tjhowse/blinker/datasheets/Supercapacitor Degradation and Life-time_files/supercapacitor-degradation-and-life-time-1140x641.jpg

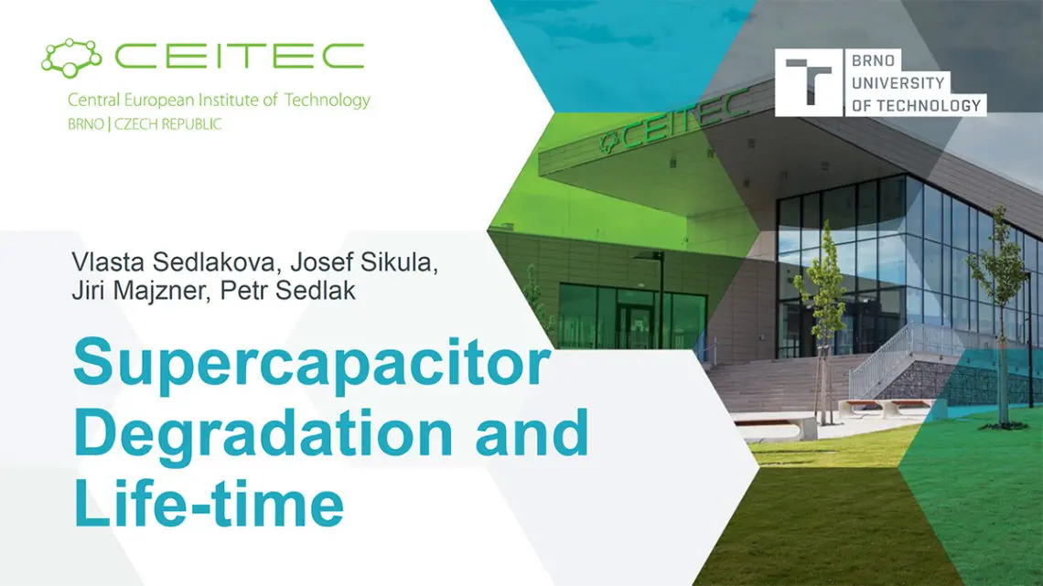
datasheets/Supercapacitor Degradation and Life-time_files/supercapacitor-degradation-and-life-time-1140x641.jpg
