tjhowse/blinker/datasheets/Supercapacitor Degradation and Life-time_files/2nd-PCNS-e-proceedings-750x595.jpg

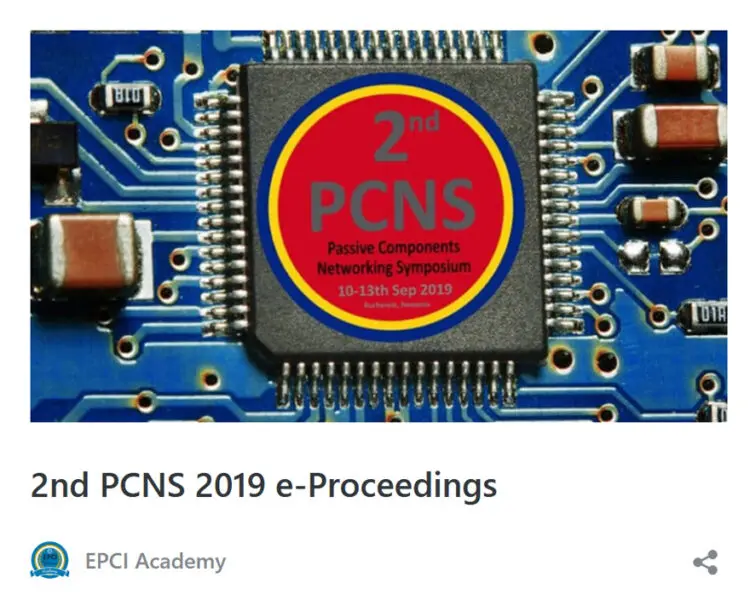
datasheets/Supercapacitor Degradation and Life-time_files/2nd-PCNS-e-proceedings-750x595.jpg
