tjhowse/blinker/datasheets/Supercapacitor Degradation and Life-time_files/CNF-MIM-world-thinnest-capacitors-350x250.jpg

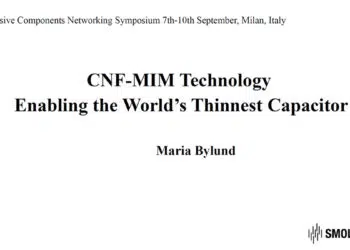
datasheets/Supercapacitor Degradation and Life-time_files/CNF-MIM-world-thinnest-capacitors-350x250.jpg
