tjhowse/blinker/datasheets/Supercapacitor Degradation and Life-time_files/development-of-3D-on-chip-capacitor-350x250.jpg

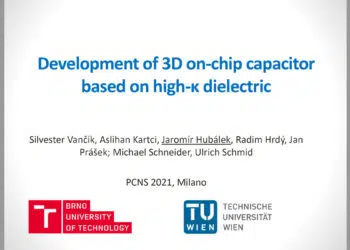
datasheets/Supercapacitor Degradation and Life-time_files/development-of-3D-on-chip-capacitor-350x250.jpg
