tjhowse/blinker/datasheets/Supercapacitor Degradation and Life-time_files/Fig1-supercapacitor-equivalent-circuit-model-300x136.png

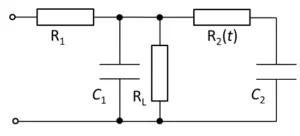
datasheets/Supercapacitor Degradation and Life-time_files/Fig1-supercapacitor-equivalent-circuit-model-300x136.png
