tjhowse/blinker/datasheets/Supercapacitor Degradation and Life-time_files/Fig-2a-supercapacitor-Helmholtz-capacitance-vs-time-of-a_002.png

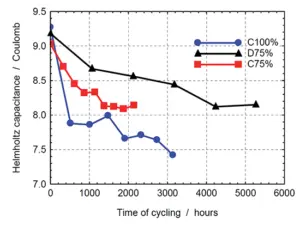
datasheets/Supercapacitor Degradation and Life-time_files/Fig-2a-supercapacitor-Helmholtz-capacitance-vs-time-of-a_002.png
