tjhowse/blinker/datasheets/Supercapacitor Degradation and Life-time_files/Fig-2b-supercapacitor-diffuse-capacitance-vs-time-of-age_002.png

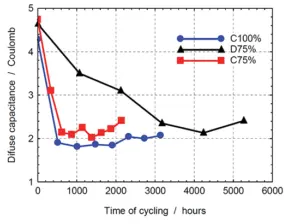
datasheets/Supercapacitor Degradation and Life-time_files/Fig-2b-supercapacitor-diffuse-capacitance-vs-time-of-age_002.png
