tjhowse/blinker/datasheets/Supercapacitor Degradation and Life-time_files/Fig-2b-supercapacitor-diffuse-capacitance-vs-time-of-ageing-.png

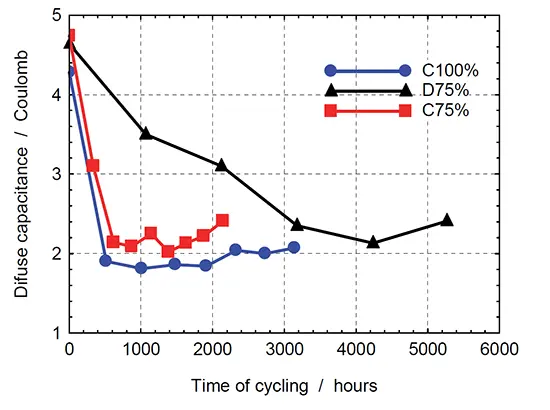
datasheets/Supercapacitor Degradation and Life-time_files/Fig-2b-supercapacitor-diffuse-capacitance-vs-time-of-ageing-.png
