tjhowse/blinker/datasheets/Supercapacitor Degradation and Life-time_files/Fig-3a-supercapacitor-diffuse-resistance-parameter-vs-ti_002.png

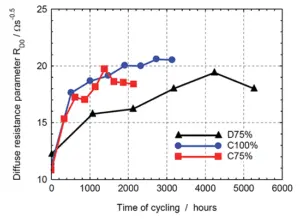
datasheets/Supercapacitor Degradation and Life-time_files/Fig-3a-supercapacitor-diffuse-resistance-parameter-vs-ti_002.png
