tjhowse/blinker/datasheets/Supercapacitor Degradation and Life-time_files/Fig-3b-supercapacitor-equivalent-series-resistance-vs-ti_002.png

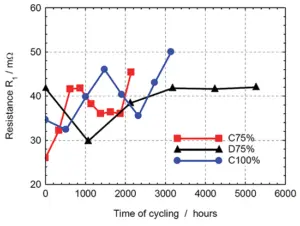
datasheets/Supercapacitor Degradation and Life-time_files/Fig-3b-supercapacitor-equivalent-series-resistance-vs-ti_002.png
