tjhowse/blinker/datasheets/Supercapacitor Degradation and Life-time_files/Fig-3b-supercapacitor-equivalent-series-resistance-vs-time-o.png

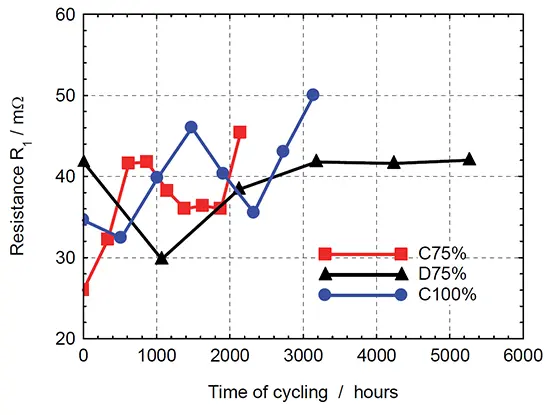
datasheets/Supercapacitor Degradation and Life-time_files/Fig-3b-supercapacitor-equivalent-series-resistance-vs-time-o.png
