tjhowse/blinker/datasheets/Supercapacitor Degradation and Life-time_files/Fig-6a-supercapacitor-DC-capacitance-vs-time-of-ageing-f_002.png

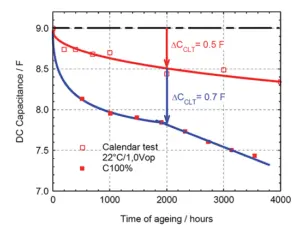
datasheets/Supercapacitor Degradation and Life-time_files/Fig-6a-supercapacitor-DC-capacitance-vs-time-of-ageing-f_002.png
