tjhowse/blinker/datasheets/Supercapacitor Degradation and Life-time_files/Fig-8-supercapacitor-DC-capacitance-relative-value-vs-ti_002.png

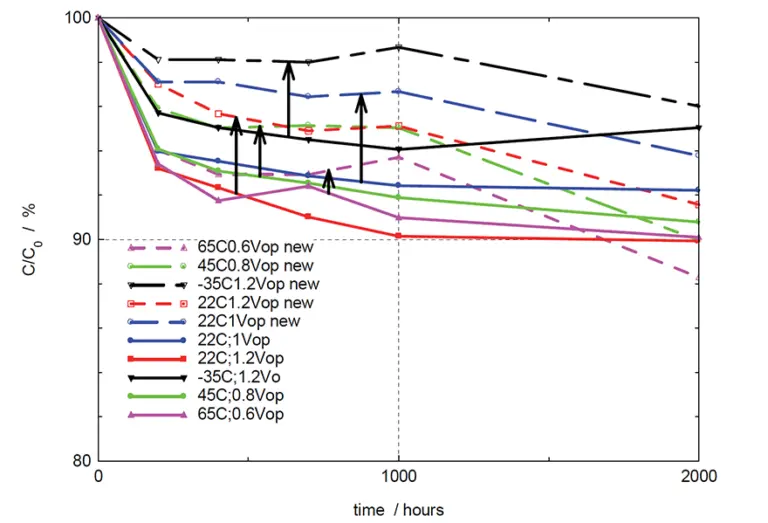
datasheets/Supercapacitor Degradation and Life-time_files/Fig-8-supercapacitor-DC-capacitance-relative-value-vs-ti_002.png
