tjhowse/blinker/datasheets/Supercapacitor Degradation and Life-time_files/Fig-9-supercapacitor-DC-capacitance-relative-value-vs-ti_003.png

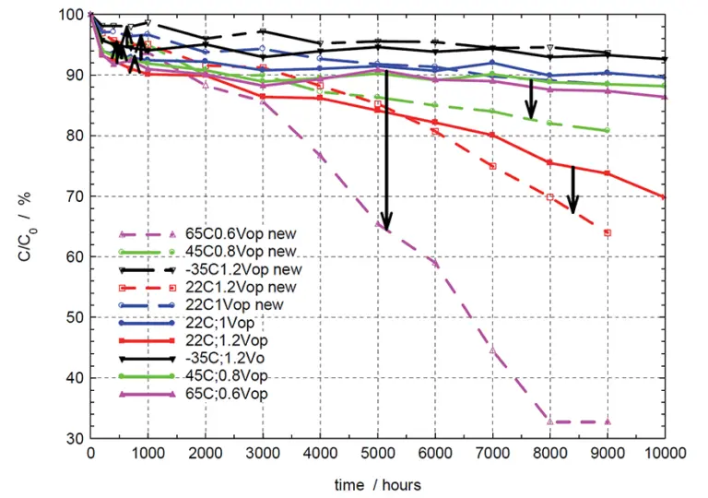
datasheets/Supercapacitor Degradation and Life-time_files/Fig-9-supercapacitor-DC-capacitance-relative-value-vs-ti_003.png
