tjhowse/blinker/datasheets/Supercapacitor Degradation and Life-time_files/Fig-10-supercapacitor-DC-capacitance-relative-value-vs-t_002.png

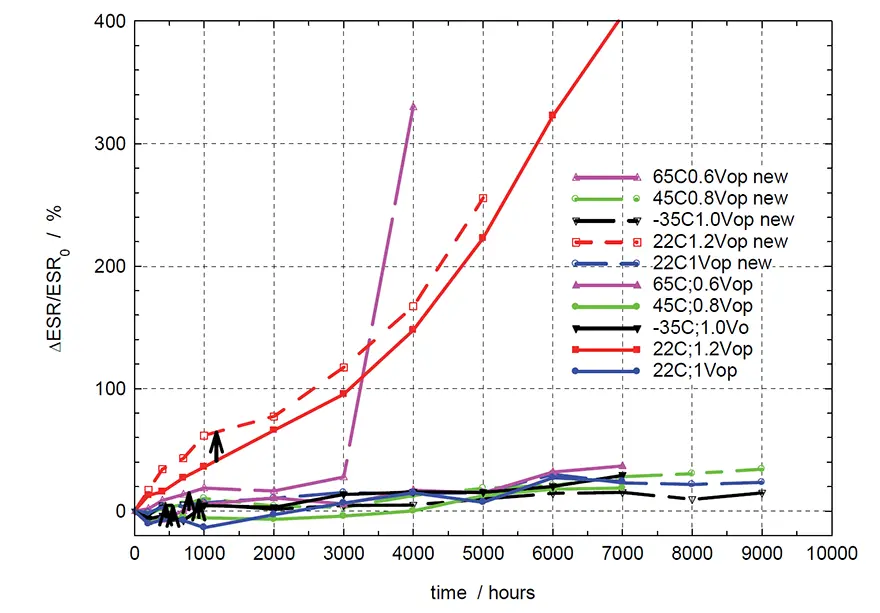
datasheets/Supercapacitor Degradation and Life-time_files/Fig-10-supercapacitor-DC-capacitance-relative-value-vs-t_002.png
