tjhowse/blinker/datasheets/Supercapacitor Degradation and Life-time_files/Way-to-high-voltage-aluminum-polymer-capacitors-350x250.jpg

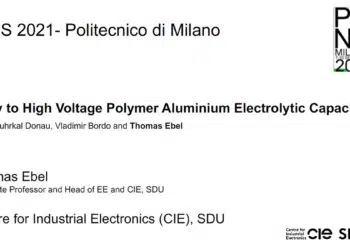
datasheets/Supercapacitor Degradation and Life-time_files/Way-to-high-voltage-aluminum-polymer-capacitors-350x250.jpg
