tjhowse/blinker/datasheets/Using Profiles – osPID_files/CompiledFrontendProfileStorage.png

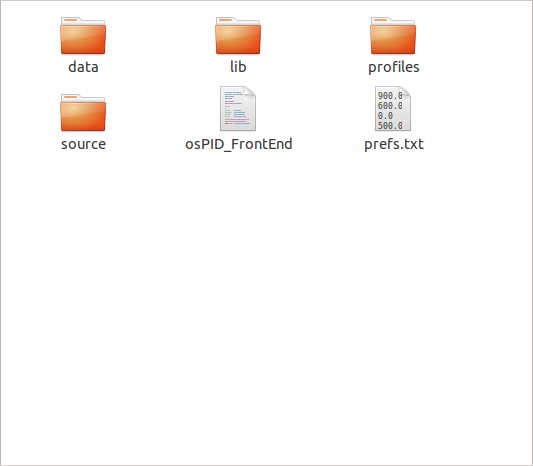
datasheets/Using Profiles – osPID_files/CompiledFrontendProfileStorage.png
