tjhowse/blinker/datasheets/Using Profiles – osPID_files/LoadingProfile.png

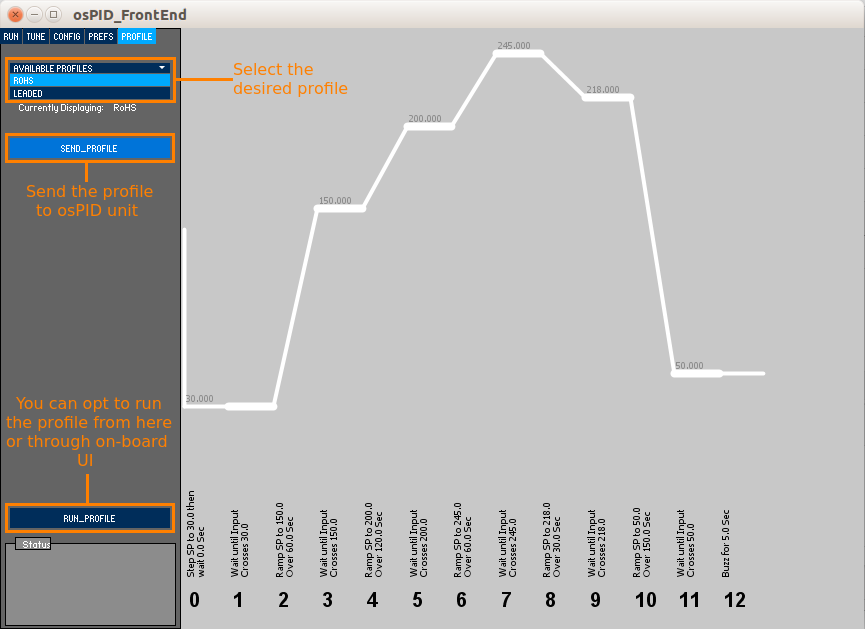
datasheets/Using Profiles – osPID_files/LoadingProfile.png
