tjhowse/blinker/datasheets/Using Profiles – osPID_files/NotCompiledFrontendProfileStorage.png

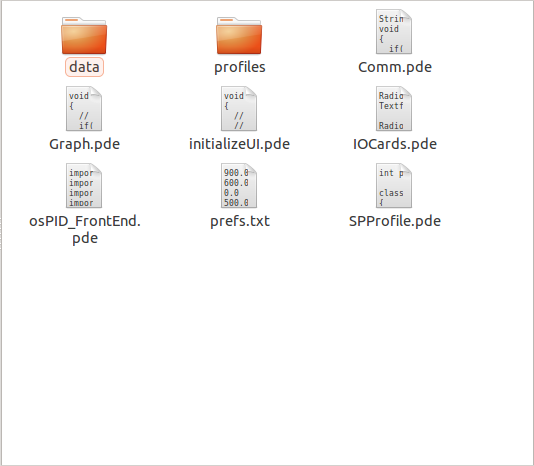
datasheets/Using Profiles – osPID_files/NotCompiledFrontendProfileStorage.png
