tjhowse/blinker/datasheets/Using Profiles – osPID_files/ProfileOnUI.jpg

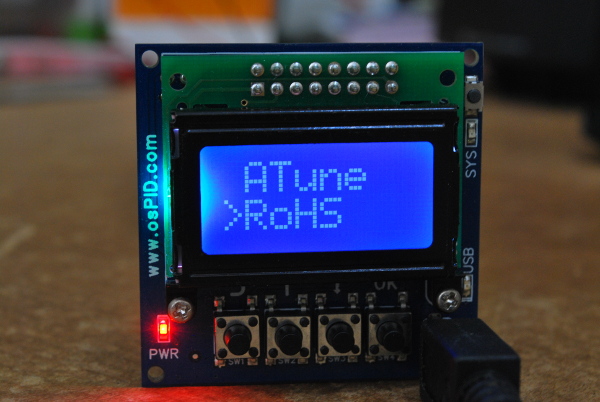
datasheets/Using Profiles – osPID_files/ProfileOnUI.jpg
