tjhowse/blinker/datasheets/Using Profiles – osPID_files/ProfilesStorage.png

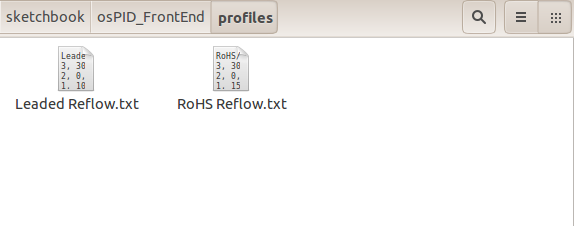
datasheets/Using Profiles – osPID_files/ProfilesStorage.png
