tjhowse/blinker/testlogs/all/22030400.CSV

START | 2022/03/04 | 10:52:23
ID | 170800000
INTERVAL | 010 | sec
 | MAIN |  |  | SUB-1 |  |  | SUB-2 |  |  | Remark
No. | Func. | Value | Unit | Func. | Value | Unit | Func. | Value | Unit
1 | DCV | 02.6524 | V
2 | DCV | 02.6513 | V
3 | DCV | 02.6497 | V
4 | DCV | 02.6482 | V
5 | DCV | 02.6468 | V
6 | DCV | 02.6454 | V
7 | DCV | 02.6440 | V
8 | DCV | 02.6426 | V
9 | DCV | 02.6414 | V
10 | DCV | 02.6402 | V
11 | DCV | 02.6390 | V
12 | DCV | 02.6378 | V
13 | DCV | 02.6368 | V
14 | DCV | 02.6356 | V
15 | DCV | 02.6347 | V
16 | DCV | 02.6335 | V
17 | DCV | 02.6326 | V
18 | DCV | 02.6317 | V
19 | DCV | 02.6307 | V
20 | DCV | 02.6298 | V
21 | DCV | 02.6289 | V
22 | DCV | 02.6281 | V
23 | DCV | 02.6273 | V
24 | DCV | 02.6265 | V
25 | DCV | 02.6256 | V
26 | DCV | 02.6247 | V
27 | DCV | 02.6240 | V
28 | DCV | 02.6231 | V
29 | DCV | 02.6225 | V
30 | DCV | 02.6216 | V
31 | DCV | 02.6209 | V
32 | DCV | 02.6201 | V
33 | DCV | 02.6195 | V
34 | DCV | 02.6188 | V
35 | DCV | 02.6182 | V
36 | DCV | 02.6175 | V
37 | DCV | 02.6168 | V
38 | DCV | 02.6162 | V
39 | DCV | 02.6156 | V
40 | DCV | 02.6149 | V
41 | DCV | 02.6143 | V
42 | DCV | 02.6138 | V
43 | DCV | 02.6132 | V
44 | DCV | 02.6124 | V
45 | DCV | 02.6119 | V
46 | DCV | 02.6114 | V
47 | DCV | 02.6108 | V
48 | DCV | 02.6103 | V
49 | DCV | 02.6098 | V
50 | DCV | 02.6091 | V
51 | DCV | 02.6085 | V
52 | DCV | 02.6081 | V
53 | DCV | 02.6076 | V
54 | DCV | 02.6070 | V
55 | DCV | 02.6065 | V
56 | DCV | 02.6061 | V
57 | DCV | 02.6056 | V
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
3266 | DCV | 02.3809 | V
3267 | DCV | 02.3809 | V
3268 | DCV | 02.3809 | V
3269 | DCV | 02.3809 | V
3270 | DCV | 02.3808 | V
3271 | DCV | 02.3808 | V
3272 | DCV | 02.3807 | V
3273 | DCV | 02.3807 | V
3274 | DCV | 02.3807 | V
3275 | DCV | 02.3807 | V
3276 | DCV | 02.3806 | V
3277 | DCV | 02.3806 | V
3278 | DCV | 02.3806 | V
MAX | 1 | DCV | 02.6524 | V
MIN | 3276 | DCV | 02.3806 | V
