tjhowse/blinker/testlogs/all/22030300.CSV

START,2022/03/03,17:33:21,
ID,170800000,
INTERVAL,010,sec,
,MAIN,,,SUB-1,,,SUB-2,,,Remark,
No. ,Func. ,Value,Unit,Func. ,Value,Unit,Func. ,Value,Unit,
1,DCV,00.0000,V,,,,,,,,
2,DCV,-00.0000,V,,,,,,,,
MAX,1,DCV,00.0000,V,
MIN,2,DCV,-00.0000,V,
