tjhowse/blinker/testlogs/all/22032500.CSV

START,2022/03/25,09:08:09,
ID,170800000,
INTERVAL,010,sec,
,MAIN,,,SUB-1,,,SUB-2,,,Remark,
No. ,Func. ,Value,Unit,Func. ,Value,Unit,Func. ,Value,Unit,
1,DCV,01.3569,V,,,,,,,,
MAX,1,DCV,01.3569,V,
MIN,1,DCV,01.3569,V,
