tjhowse/blinker/code/blinker/sequence.h

// did you ever hear the tragedy of darth plagueis the wise i thought not its not a story the jedi would tell you its a sith legend darth plagueis was a dark lord of the sith so powerful and so wise he could use the force to influence the midichlorians to create life did you ever hear the tragedy of darth plagueis the wise i thought not its not a story the jedi would tell you its a sith legend darth plagueis was a dark lord of the sith so powerful and so wise he could use the force to influence the midichlorians to create life did you ever hear the tragedy of darth plagueis the wise i thought not its not a story the jedi would tell you ff
uint8_t const sequence[] = {0x57, 0x14, 0x57, 0xc0, 0x75, 0xc7, 0xdd, 0x51, 0x07, 0x44, 0x75, 0x44, 0x17, 0x50, 0x45, 0x74, 0x74, 0x01, 0x47, 0x15, 0x01, 0x47, 0x17, 0x1d, 0x77, 0x11, 0x57, 0x5c, 0x77, 0xc0, 0xdd, 0x51, 0x17, 0x70, 0x45, 0x47, 0x17, 0x47, 0x15, 0xd0, 0x5d, 0x74, 0x45, 0xc7, 0x5d, 0xd4, 0x11, 0x45, 0x05, 0x1c, 0x55, 0x04, 0x74, 0x47, 0x51, 0x11, 0x50, 0xc0, 0x51, 0xc5, 0xdd, 0x51, 0xc7, 0x5d, 0x54, 0x71, 0xc0, 0xc5, 0xdd, 0x71, 0x40, 0x71, 0x54, 0xc0, 0xc5, 0xdd, 0x71, 0x40, 0x07, 0x54, 0x1c, 0x77, 0x47, 0x17, 0xd7, 0x1d, 0x70, 0x54, 0x11, 0xd0, 0xdd, 0x11, 0x57, 0x14, 0xd0, 0x1d, 0x77, 0x47, 0x1d, 0x5d, 0x71, 0x05, 0x1c, 0xd1, 0x15, 0x5d, 0x01, 0xd7, 0x1d, 0x77, 0x47, 0x1d, 0x50, 0x1c, 0x15, 0xd0, 0x01, 0x15, 0xc5, 0x51, 0x05, 0x74, 0x45, 0xdc, 0x45, 0x5c, 0x5c, 0x01, 0x57, 0x74, 0x74, 0x71, 0x54, 0x01, 0xdd, 0x45, 0x57, 0x74, 0xdc, 0x45, 0x1d, 0x51, 0x54, 0x40, 0x77, 0x74, 0x54, 0x40, 0x07, 0x5c, 0xd1, 0xd1, 0xc5, 0x75, 0x40, 0x57, 0xdc, 0x1d, 0x5d, 0x5c, 0x01, 0x77, 0x47, 0x5d, 0xc0, 0x51, 0x45, 0x40, 0x45, 0x71, 0x54, 0x01, 0x15, 0x77, 0x07, 0x74, 0x17, 0x77, 0x47, 0x77, 0x44, 0x17, 0x75, 0x51, 0x47, 0x57, 0x40, 0xc7, 0xc5, 0x15, 0x50, 0x71, 0x77, 0x40, 0x77, 0x14, 0x15, 0x01, 0x55, 0x04, 0x5c, 0x17, 0x77, 0x47, 0x1d, 0x5d, 0x71, 0x05, 0xd4, 0x51, 0x11, 0x70, 0x54, 0x11, 0x50, 0x17, 0x77, 0x47, 0x17, 0xd7, 0x45, 0xc0, 0x71, 0x77, 0x40, 0x71, 0x51, 0x17, 0x5d, 0x51, 0x47, 0x5c, 0x5c, 0x17, 0x01, 0x47, 0x15, 0x01, 0x77, 0x14, 0x57, 0x14, 0xd7, 0x45, 0x15, 0x5d, 0x71, 0x77, 0x74, 0x51, 0x74, 0x5c, 0x54, 0xc0, 0x71, 0x77, 0xc0, 0x75, 0xd1, 0x45, 0x74, 0x1c, 0x01, 0x5d, 0x51, 0xd4, 0x45, 0xc0, 0x15, 0xc5, 0x15, 0x70, 0xdd, 0x71, 0x77, 0xd4, 0x01, 0x51, 0x1d, 0xd1, 0x05, 0x54, 0x11, 0x1d, 0x5d, 0xc0, 0x51, 0x45, 0xc0, 0xd1, 0x45, 0xc7, 0x5d, 0xc4, 0x15, 0xd7, 0x1d, 0x70, 0x77, 0xd4, 0x05, 0x5c, 0xd1, 0xd1, 0xc5, 0x51, 0x05, 0x74, 0x17, 0x5d, 0xd1, 0x71, 0x17, 0x75, 0x44, 0x51, 0x01, 0x47, 0x15, 0x01, 0xdd, 0x51, 0x54, 0x04, 0x14, 0x70, 0x54, 0x71, 0x77, 0xd4, 0x71, 0x17, 0x55, 0x1c, 0x70, 0x71, 0x77, 0x1c, 0x50, 0x1c, 0x15, 0x70, 0x71, 0x77, 0x1c, 0xd0, 0x01, 0x15, 0xc7, 0xdd, 0xd1, 0xc5, 0x75, 0x07, 0x1c, 0x55, 0x04, 0x74, 0x77, 0xc4, 0x15, 0x05, 0x74, 0xc7, 0xdd, 0x51, 0x47, 0x57, 0x5c, 0x01, 0x47, 0x74, 0x45, 0x57, 0xc0, 0x75, 0xc7, 0xdd, 0x51, 0x07, 0x14, 0x47, 0x05, 0x74, 0x40, 0x45, 0x71, 0x54, 0x01, 0x5d, 0x11, 0x77, 0x11, 0x17, 0x57, 0xc0, 0x15, 0x1d, 0x5d, 0x1c, 0x55, 0x40, 0x77, 0xd1, 0x15, 0x1d, 0x77, 0x51, 0x47, 0x14, 0x15, 0xd0, 0x1d, 0x1d, 0x15, 0xd0, 0x01, 0x57, 0x74, 0x74, 0x71, 0x1d, 0xd0, 0x15, 0x77, 0x47, 0x17, 0x57, 0xc0, 0xdd, 0x51, 0x17, 0x70, 0x54, 0x11, 0x50, 0x51, 0x1c, 0x55, 0x40, 0xc5, 0xdd, 0x01, 0xdd, 0xc5, 0xdd, 0xd1, 0x1d, 0xd1, 0x45, 0x5d, 0xd4, 0xd1, 0x15, 0xd0, 0x71, 0x71, 0x05, 0x54, 0xdc, 0x1d, 0xd0, 0x1d, 0x45, 0x45, 0x40, 0x15, 0x01, 0xd7, 0xc5, 0xdd, 0x51, 0x47, 0x57, 0x5c, 0x01, 0x75, 0x54, 0x04, 0x1c, 0x55, 0x04, 0xd4, 0xc5, 0xdd, 0xd1, 0xc5, 0x75, 0x11, 0x70, 0xdc, 0x1d, 0x50, 0x5c, 0xd4, 0x45, 0x57, 0xd4, 0x11, 0x17, 0xd7, 0x45, 0xc0, 0x51, 0x45, 0xc0, 0x1d, 0xc5, 0x15, 0xc5, 0x75, 0x51, 0x45, 0x57, 0xdc, 0x1d, 0x5d, 0x14, 0x1d, 0x17, 0x15, 0x70, 0xdc, 0x1d, 0x70, 0x5d, 0x74, 0x11, 0x1d, 0x47, 0x40, 0x57, 0x14, 0x75, 0x11, 0x70, 0x45, 0x71, 0x05, 0x5c, 0x77, 0xdc, 0x1d, 0x75, 0x40, 0x54, 0x47, 0x74, 0x01, 0x55, 0x44, 0x47, 0x17, 0x70, 0x54, 0x11, 0x70, 0x74, 0xd1, 0x71, 0x17, 0x71, 0xc5, 0x75, 0x07, 0xdc, 0x1d, 0x75, 0x01, 0x57, 0x74, 0x74, 0x71, 0x54, 0x01, 0xdd, 0x45, 0x57, 0x74, 0xdc, 0x45, 0x1d, 0x51, 0x54, 0xc0, 0x51, 0x45, 0x40, 0x77, 0x14, 0x15, 0x01, 0x05, 0x1c, 0x55, 0xdc, 0x1d, 0x75, 0xdc, 0x45, 0x15, 0x07, 0x5c, 0xdc, 0x1d, 0x07, 0x14, 0x47, 0x05, 0x5c, 0xdc, 0x1d, 0x07, 0x74, 0x40, 0xc5, 0x71, 0x77, 0x74, 0x71, 0xdd, 0x01, 0x47, 0x15, 0x01, 0xdd, 0x1d, 0x71, 0x45, 0x01, 0xdd, 0x71, 0x77, 0xd4, 0xd1, 0x15, 0x57, 0xc0, 0x11, 0x5d, 0xd1, 0x15, 0x70, 0xdd, 0x71, 0x77, 0xd4, 0x01, 0x75, 0x51, 0x17, 0x00};
