tjhowse/blinker/code/blinker/message.h

//  SPHINX OF BLACK QUARTZ, JUDGE MY VOW! 0123456789 
const uint8_t message[] = {0xc0, 0x0c, 0xa3, 0xa9, 0x8b, 0x03, 0xaf, 0x09, 0x88, 0x6c, 0x38, 0xae, 0x40, 0x5c, 0x87, 0x32, 0xad, 0x33, 0x80, 0x5a, 0x93, 0x67, 0x09, 0xb4, 0x39, 0x60, 0xbf, 0x77, 0x00, 0x40, 0x91, 0x34, 0x51, 0x95, 0x75, 0x61, 0x19, 0x00};
